AlicDanclic/Signal_and_Communication_ElecCompetition_Learning/Bitmap/50Ohm阻抗匹配.png

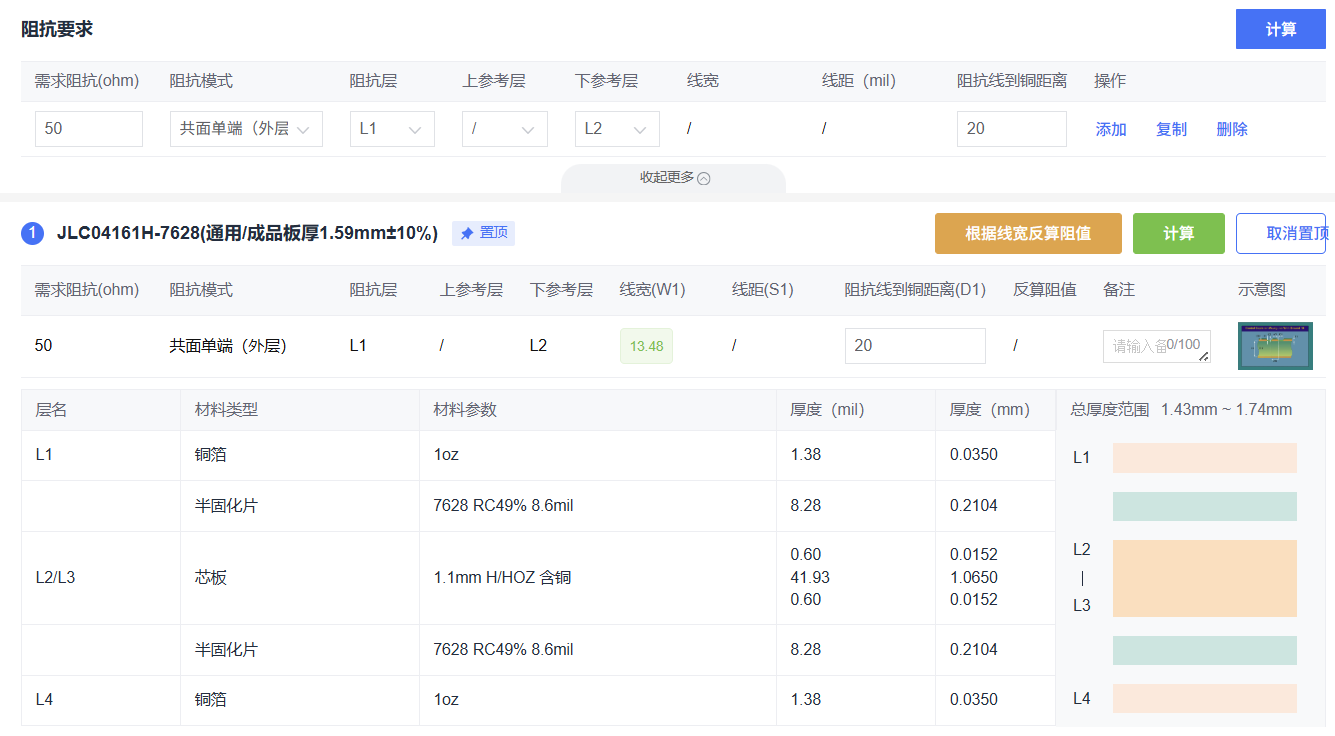
Bitmap/50Ohm阻抗匹配.png
