AlicDanclic/Signal_and_Communication_ElecCompetition_Learning/Bitmap/Attenuator底层.png

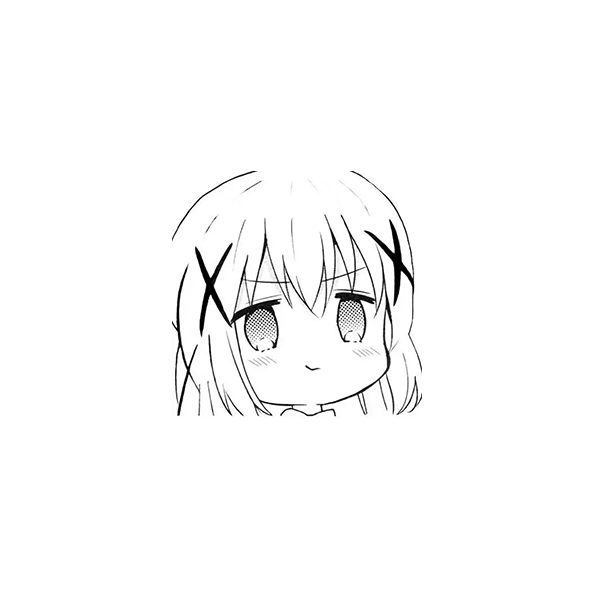
Bitmap/Attenuator底层.png
