AlicDanclic/Signal_and_Communication_ElecCompetition_Learning/Bitmap/Attenuator顶层.png

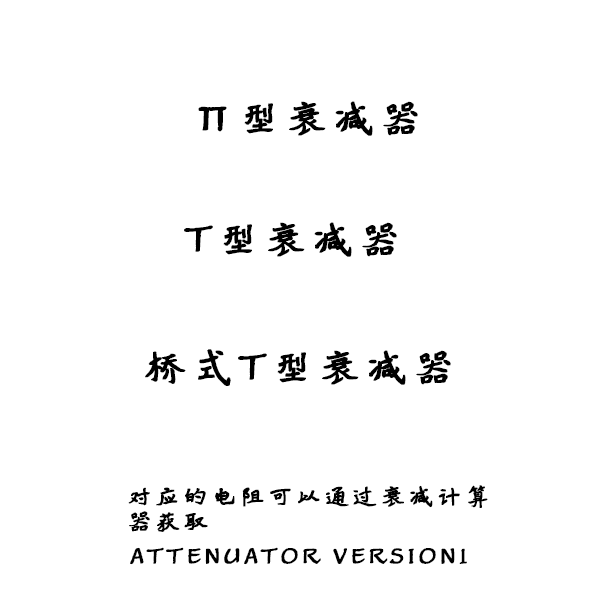
Bitmap/Attenuator顶层.png
