AlicDanclic/Signal_and_Communication_ElecCompetition_Learning/Bitmap/Dual_OutputLDO顶层.png

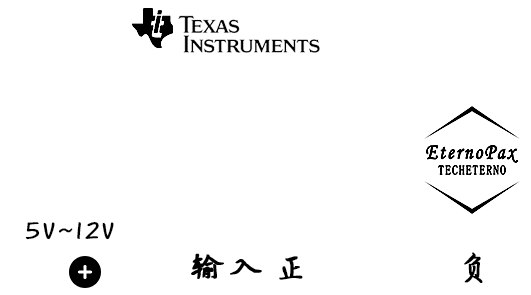
Bitmap/Dual_OutputLDO顶层.png
