AlicDanclic/Signal_and_Communication_ElecCompetition_Learning/Bitmap/FPGA扩展板框图.png

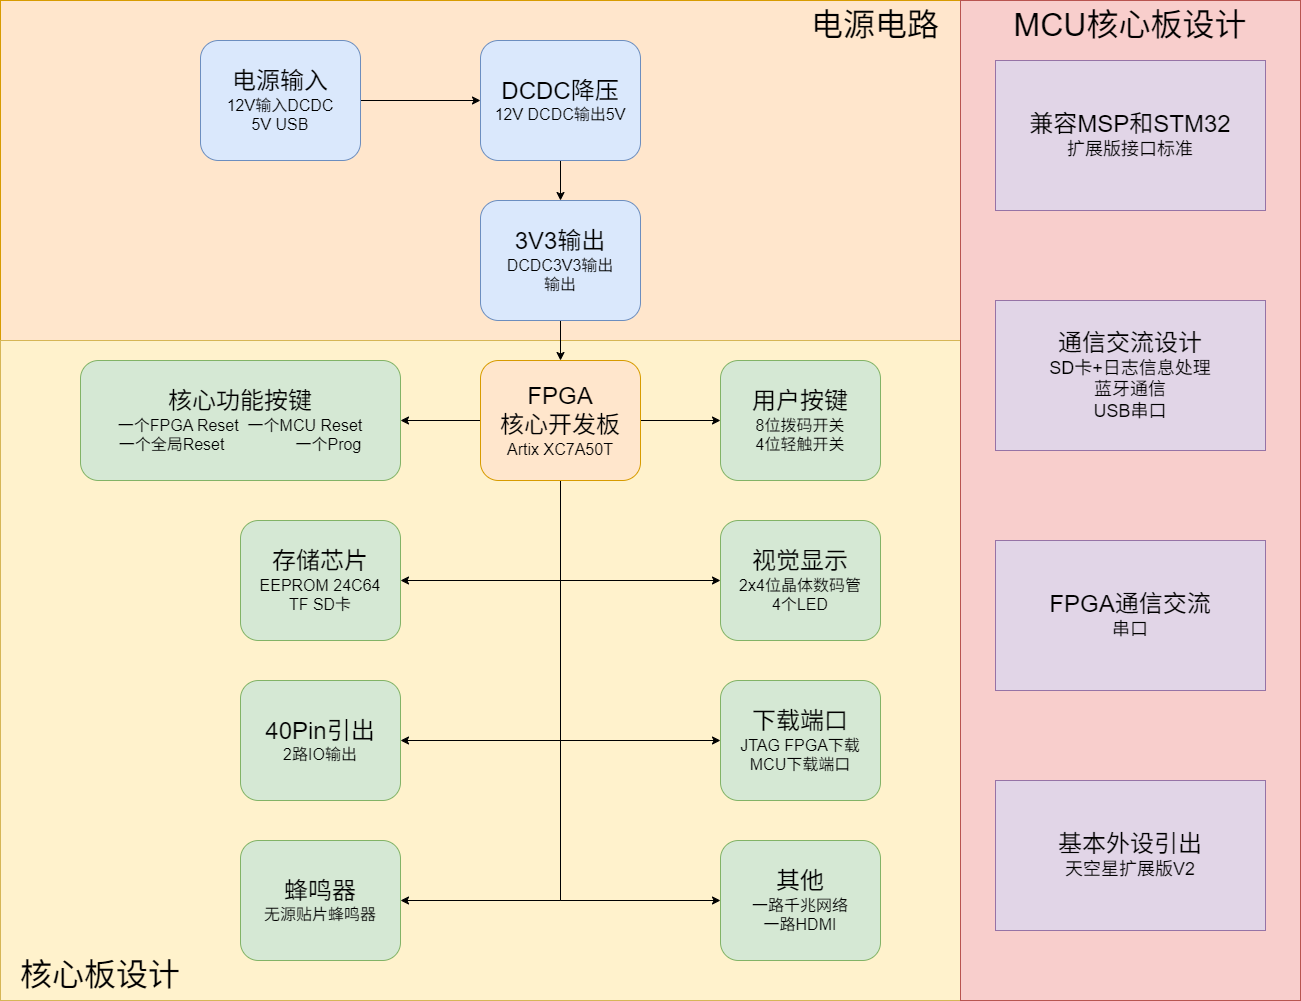
Bitmap/FPGA扩展板框图.png
