AlicDanclic/Signal_and_Communication_ElecCompetition_Learning/Bitmap/LDO底层.png

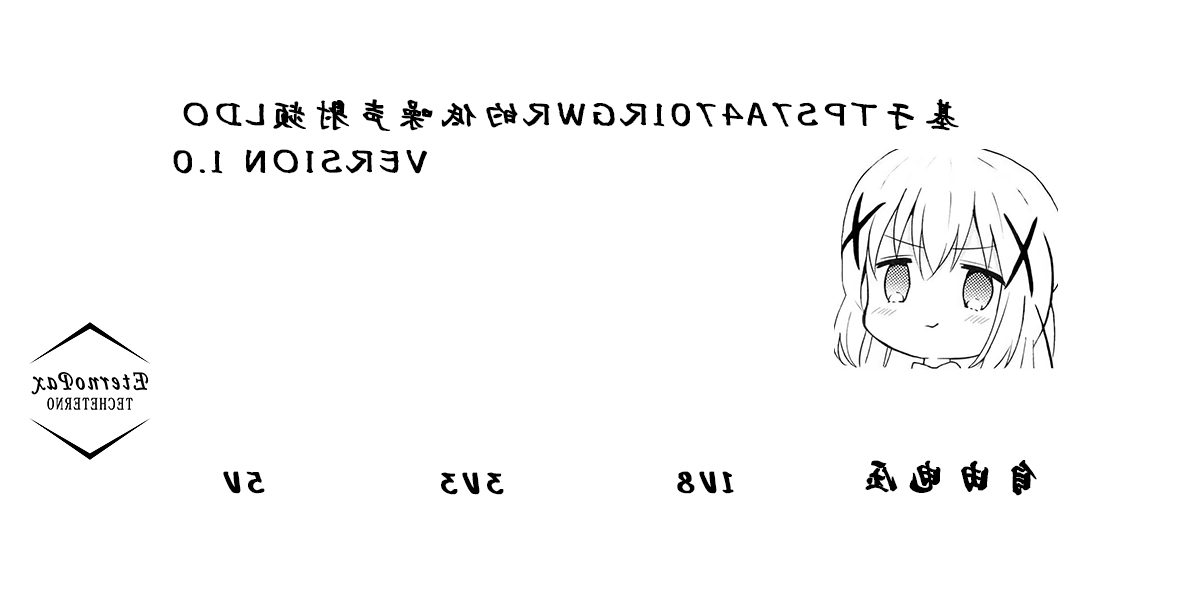
Bitmap/LDO底层.png
