AlicDanclic/Signal_and_Communication_ElecCompetition_Learning/Bitmap/LDO顶层.png

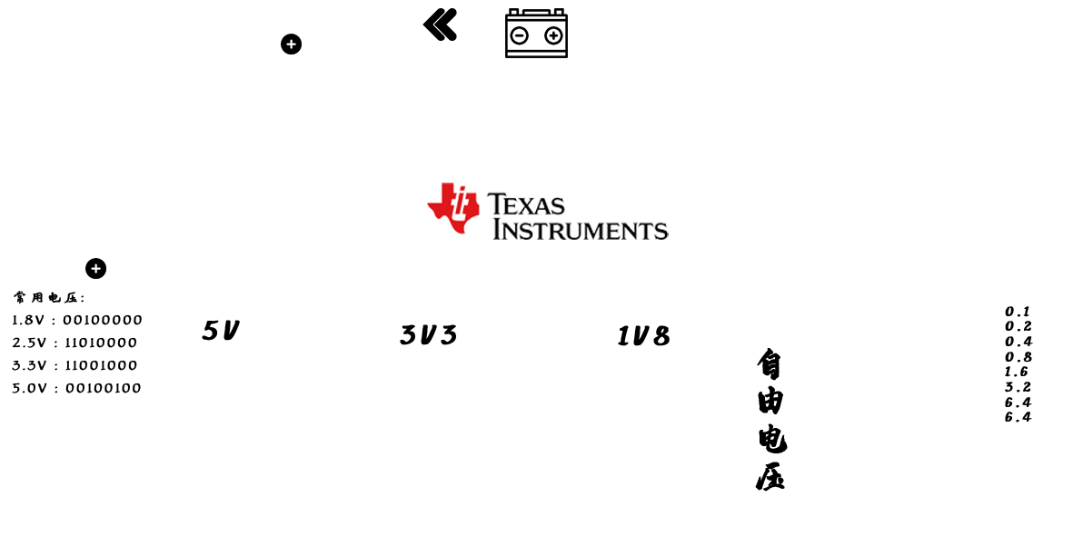
Bitmap/LDO顶层.png
