AlicDanclic/Signal_and_Communication_ElecCompetition_Learning/Bitmap/LM27762布局.png

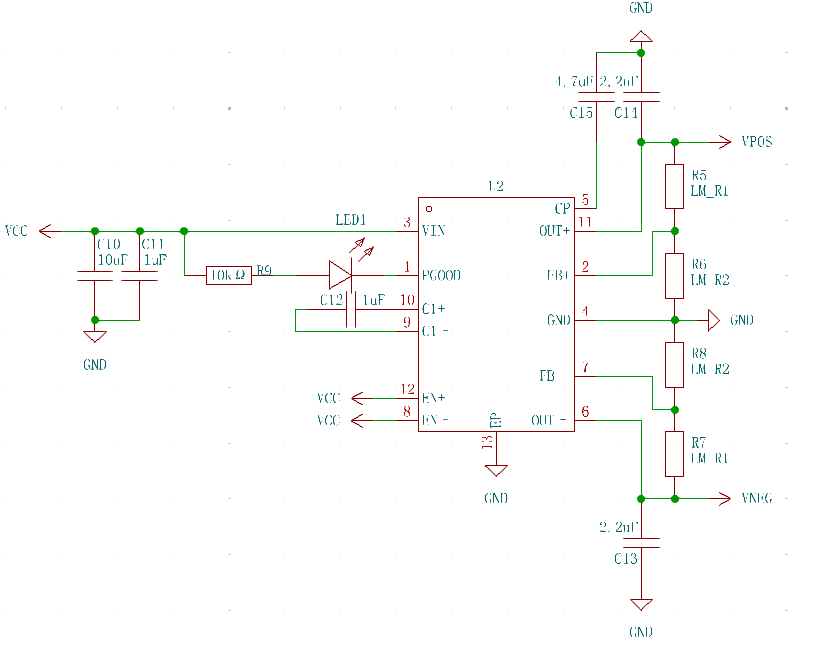
Bitmap/LM27762布局.png
