AlicDanclic/Signal_and_Communication_ElecCompetition_Learning/Bitmap/reflective_attenuator.png

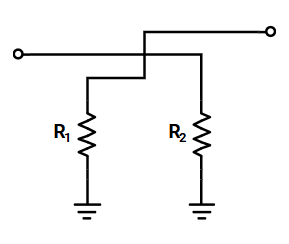
Bitmap/reflective_attenuator.png
