AlicDanclic/Signal_and_Communication_ElecCompetition_Learning/Bitmap/RF_DualSwitch顶层.png

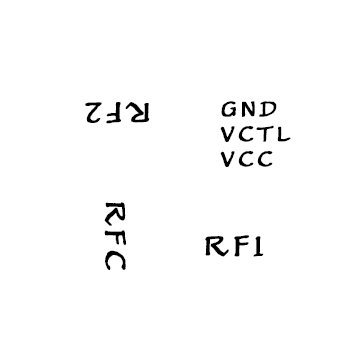
Bitmap/RF_DualSwitch顶层.png
