AlicDanclic/Signal_and_Communication_ElecCompetition_Learning/Bitmap/RF_TribeSwitch.png

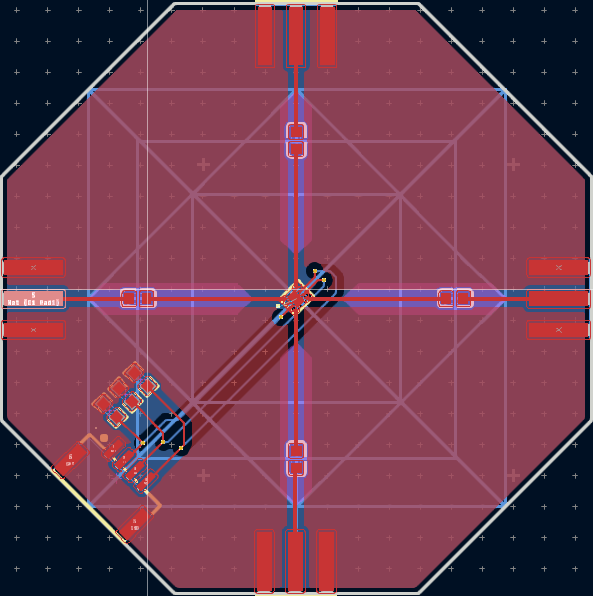
Bitmap/RF_TribeSwitch.png
