AlicDanclic/Signal_and_Communication_ElecCompetition_Learning/Bitmap/RF_TribeSwitch顶层.png

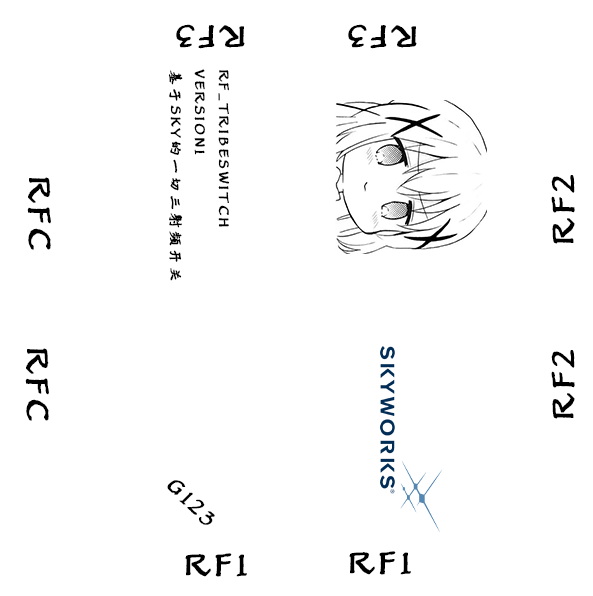
Bitmap/RF_TribeSwitch顶层.png
