AlicDanclic/Signal_and_Communication_ElecCompetition_Learning/Bitmap/八卦图.jpg

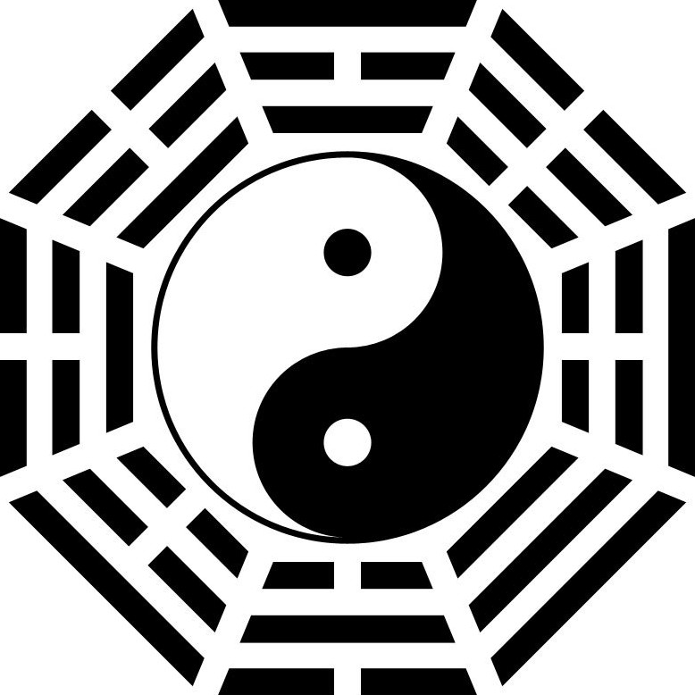
Bitmap/八卦图.jpg
