AlicDanclic/Signal_and_Communication_ElecCompetition_Learning/Bitmap/嘉立创.png

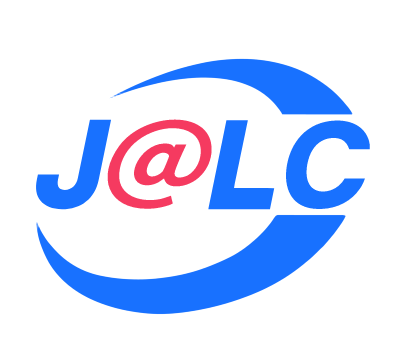
Bitmap/嘉立创.png
