AlicDanclic/Signal_and_Communication_ElecCompetition_Learning/Bitmap/左.png

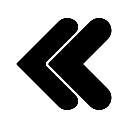
Bitmap/左.png
