AlicDanclic/Signal_and_Communication_ElecCompetition_Learning/Bitmap/开关.png

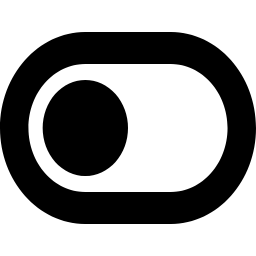
Bitmap/开关.png
