AlicDanclic/Signal_and_Communication_ElecCompetition_Learning/Bitmap/智乃智乃.png

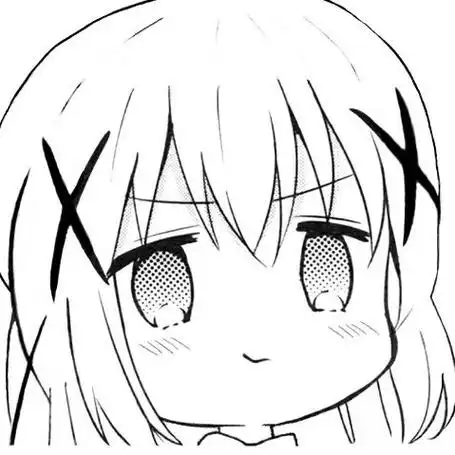
Bitmap/智乃智乃.png
