AlicDanclic/Signal_and_Communication_ElecCompetition_Learning/Bitmap/正电源.png

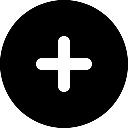
Bitmap/正电源.png
