AlicDanclic/Signal_and_Communication_ElecCompetition_Learning/Bitmap/正负电源LDO.png

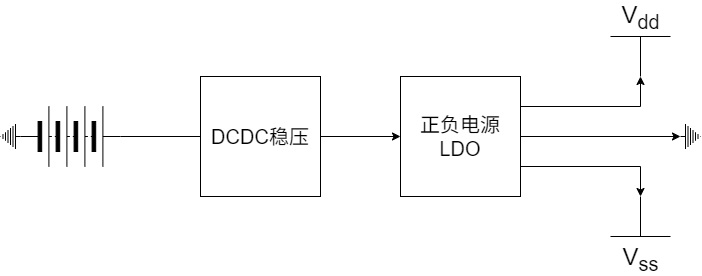
Bitmap/正负电源LDO.png
