AlicDanclic/Signal_and_Communication_ElecCompetition_Learning/Bitmap/电插头-128x128.png

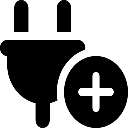
Bitmap/电插头-128x128.png
