AlicDanclic/Signal_and_Communication_ElecCompetition_Learning/Bitmap/电池-128x128.png

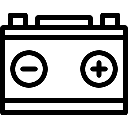
Bitmap/电池-128x128.png
